xiaokaizip/lm5116-digital-power/c6t6-lm5116/Core/Src/oled.c

//
// Created by LaoZhu on 2022/3/3.
//

#include "oled.h"
#include "iic.h"
#include "data_type_conversion.h"
#include "stm32f1xx_hal.h"

const unsigned char F8X16[] = {
        0x00, 0x00, 0x00, 0x00, 0x00, 0x00, 0x00, 0x00, 0x00, 0x00, 0x00, 0x00, 0x00, 0x00, 0x00, 0x00,// 0
        0x00, 0x00, 0x00, 0xF8, 0x00, 0x00, 0x00, 0x00, 0x00, 0x00, 0x00, 0x33, 0x30, 0x00, 0x00, 0x00,//! 1
        0x00, 0x10, 0x0C, 0x06, 0x10, 0x0C, 0x06, 0x00, 0x00, 0x00, 0x00, 0x00, 0x00, 0x00, 0x00, 0x00,//" 2
        0x40, 0xC0, 0x78, 0x40, 0xC0, 0x78, 0x40, 0x00, 0x04, 0x3F, 0x04, 0x04, 0x3F, 0x04, 0x04, 0x00,//# 3
        0x00, 0x70, 0x88, 0xFC, 0x08, 0x30, 0x00, 0x00, 0x00, 0x18, 0x20, 0xFF, 0x21, 0x1E, 0x00, 0x00,//$ 4
        0xF0, 0x08, 0xF0, 0x00, 0xE0, 0x18, 0x00, 0x00, 0x00, 0x21, 0x1C, 0x03, 0x1E, 0x21, 0x1E, 0x00,//% 5
        0x00, 0xF0, 0x08, 0x88, 0x70, 0x00, 0x00, 0x00, 0x1E, 0x21, 0x23, 0x24, 0x19, 0x27, 0x21, 0x10,//& 6
        0x10, 0x16, 0x0E, 0x00, 0x00, 0x00, 0x00, 0x00, 0x00, 0x00, 0x00, 0x00, 0x00, 0x00, 0x00, 0x00,//' 7
        0x00, 0x00, 0x00, 0xE0, 0x18, 0x04, 0x02, 0x00, 0x00, 0x00, 0x00, 0x07, 0x18, 0x20, 0x40, 0x00,//( 8
        0x00, 0x02, 0x04, 0x18, 0xE0, 0x00, 0x00, 0x00, 0x00, 0x40, 0x20, 0x18, 0x07, 0x00, 0x00, 0x00,//) 9
        0x40, 0x40, 0x80, 0xF0, 0x80, 0x40, 0x40, 0x00, 0x02, 0x02, 0x01, 0x0F, 0x01, 0x02, 0x02, 0x00,//* 10
        0x00, 0x00, 0x00, 0xF0, 0x00, 0x00, 0x00, 0x00, 0x01, 0x01, 0x01, 0x1F, 0x01, 0x01, 0x01, 0x00,//+ 11
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
    IIC_Wait_Ask();
    IIC_Stop();
}

void WriteDat(unsigned char data) {
    IIC_Start();
    IIC_WriteByte(0x78);
    IIC_Wait_Ask();
    IIC_WriteByte(0x40);
    IIC_Wait_Ask();
    IIC_WriteByte(data);
    IIC_Wait_Ask();
    IIC_Stop();
}

void OLED_Init(void) {
    HAL_Delay(100);

    WriteCmd(0xAE); //display off
    WriteCmd(0x20); //Set Memory Addressing Mode
    WriteCmd(0x10); //00Horizontal Addressing Mode;01Vertical Addressing Mode;10Page Addressing Mode (RESET);
    WriteCmd(0xb0); //Set Page Start Address for Page Addressing Mode,0-7
    WriteCmd(0xc8); //Set COM Output Scan Direction
    WriteCmd(0x00); //---set low column address
    WriteCmd(0x10); //---set high column address
    WriteCmd(0x40); //--set start line address
    WriteCmd(0x81); //--set contrast control register
    WriteCmd(0xff); //亮度调节 0x00~0xff
    WriteCmd(0xa1); //--set segment re-map 0 to 127
    WriteCmd(0xa6); //--set normal display
    WriteCmd(0xa8); //--set multiplex ratio(1 to 64)
    WriteCmd(0x3F); //
    WriteCmd(0xa4); //0xa4,Output follows RAM content;0xa5,Output ignores RAM content
    WriteCmd(0xd3); //-set display offset
    WriteCmd(0x00); //-not offset
    WriteCmd(0xd5); //--set display clock divide ratio/oscillator frequency
    WriteCmd(0xf0); //--set divide ratio
    WriteCmd(0xd9); //--set pre-charge period
    WriteCmd(0x22); //
    WriteCmd(0xda); //--set com pins hardware configuration
    WriteCmd(0x12);
    WriteCmd(0xdb); //--set vcomh
    WriteCmd(0x20); //0x20,0.77xVcc
    WriteCmd(0x8d); //--set DC-DC enable
    WriteCmd(0x14); //
    WriteCmd(0xaf); //--turn on oled panel
}

void OLED_SetPos(unsigned char x, unsigned char y) {
    WriteCmd(0xb0 + y);
    WriteCmd(((x & 0xf0) >> 4) | 0x10);
    WriteCmd((x & 0x0f) | 0x01);
}

void OLED_Fill(unsigned char fill_Data) {
    unsigned char m, n;
    for (m = 0; m < 8; m++) {
        WriteCmd(0xb0 + m);       //page0-page1
        WriteCmd(0x00);     //low column start address
        WriteCmd(0x10);     //high column start address
        for (n = 0; n < 128; n++) {
            WriteDat(fill_Data);
        }
    }
}

void OLED_ShowStr(unsigned char x, unsigned char y, const char *ch) {
    unsigned char c = 0, i = 0, j = 0;
    while (ch[j] != '\0') {
        c = ch[j] - 32;
        if (x > 120) {
            x = 0;
            y++;
        }
        OLED_SetPos(x, y);
        for (i = 0; i < 8; i++)
            WriteDat(F8X16[c * 16 + i]);
        OLED_SetPos(x, y + 1);
        for (i = 0; i < 8; i++)
            WriteDat(F8X16[c * 16 + i + 8]);
        x += 8;
        j++;
    }
}

void OLED_ShowFloat(unsigned char x, unsigned char y, float num) {
    char string[20];
    numTostring(num, string);
    OLED_ShowStr(x, y, string);
}

void OLED_ShowMenu(float expect_voltage, float real_voltage) {
    OLED_ShowStr(0, 0, "Expect: ");
    OLED_ShowFloat(8 * 8, 0, expect_voltage);
    OLED_ShowStr(0, 2, "Real: ");
    OLED_ShowFloat(8 * 8, 2, real_voltage);
}
