xiaokaizip/lm5116-digital-power/c6t6-lm5116/Core/Inc/data_type_conversion.h

//
// Created by 86136 on 2022/10/10.
//

#ifndef C6T6_LM5116_DATA_TYPE_CONVERSION_H
#define C6T6_LM5116_DATA_TYPE_CONVERSION_H

void numTostring(float num, char str[10]);

#endif //C6T6_LM5116_DATA_TYPE_CONVERSION_H
