xiaokaizip/lm5116-digital-power/c6t6-lm5116/Core/Inc/key.h

//
// Created by 86136 on 2022/10/15.
//

#ifndef C6T6_LM5116_KEY_H
#define C6T6_LM5116_KEY_H

#include "main.h"

#define RESISTANCE_UP         1
#define RESISTANCE_DOWN       2
#define ENTER                 3
#define SELECT                4

#define VOLTAGE_UP            2
#define VOLTAGE_DOWN          1

uint8_t Enter_Key();


#endif //C6T6_LM5116_KEY_H
