xiaokaizip/lm5116-digital-power/c6t6-lm5116/Core/Inc/oled.h

//
// Created by LaoZhu on 2022/3/3.
//

#ifndef PROGRAM_OLED_H
#define PROGRAM_OLED_H

void OLED_Fill(unsigned char fill_Data);

void OLED_ShowStr(unsigned char x, unsigned char y, const char *ch);

void OLED_ShowFloat(unsigned char x, unsigned char y, float num);

void OLED_ShowMenu(float expect_voltage, float real_voltage);

void OLED_Init(void);

#endif //PROGRAM_OLED_H
