xiaokaizip/lm5116-digital-power/c6t6-lm5116/Core/Inc/printf.h

//
// Created by 86136 on 2022/8/23.
//

#ifndef RCT6_PRINTF_H
#define RCT6_PRINTF_H

int uint8Toint(uint8_t buff);

int uint16Toint(uint16_t buff);

int uint32Toint(uint32_t buff);

void uint8PrintIn(uint8_t num);

void uint16PrintIn(uint16_t num);

void uint32PrintIn(uint32_t num);

#endif //RCT6_PRINTF_H
