xiaokaizip/lm5116-digital-power/c6t6-lm5116/Core/Src/delay.c

/**
 * There is the function of delay in this file.
 */

#include "main.h"

static unsigned int delay_us_factor = 0;

void delayus(unsigned int xus) {
    delay_us_factor = SystemCoreClock / 1000000;
    unsigned int Ticks, Time_Old, Time_Now, Time_Count = 0;
    unsigned int Reload = SysTick->LOAD;
    Ticks = xus * delay_us_factor;
    Time_Old = SysTick->VAL;
    while (1) {
        Time_Now = SysTick->VAL;
        if (Time_Now != Time_Old) {
            if (Time_Now < Time_Old)
                Time_Count += Time_Old - Time_Now;
            else
                Time_Count += Reload - Time_Now + Time_Old;
            Time_Old = Time_Now;
            if (Time_Count >= Ticks)
                break;
        }
    }
}
