xiaokaizip/lm5116-digital-power/c6t6-lm5116/Core/Src/printf.c

#include "usart.h"
#include <math.h>

/**
 * 将8位的无符号整型转化为整型
 * @param buff
 * @return
 */
int uint8Toint(uint8_t buff) {
    int num = 0;
    for (int i = 0; i < 8; i++) {
        if (buff & (1 << i)) {
            num += pow(2, i);
        }
    }
    return num;
}

/**
 * 将16位的无符号整型转化为整型
 * @param buff
 * @return
 */
int uint16Toint(uint16_t buff) {

    int num = 0;
    for (int i = 0; i < 16; i++) {
        if (buff & (1 << i)) {
            num += pow(2, i);
        }
    }
    return num;
}

/**
 * 将32位的无符号整型转化为整型
 * @param buff
 * @return
 */
int uint32Toint(uint32_t buff) {

    int num = 0;
    for (int i = 0; i < 32; i++) {
        if (buff & (1 << i)) {
            num += pow(2, i);
        }
    }
    return num;
}

/**
 * 将8位的无符号数据转换为字符串，并通过串口输出(0~255)
 * @param buff
 */
void uint8PrintIn(uint8_t num) {
    char ch[10];
    int i = 0;
    while (1) {
        if (num < 10) {
            break;
        }
        ch[i] = '0' + num % 10;
        i++;
        num /= 10;

    }
    ch[i] = '0' + num % 10;
    for (int j = 0; j < (i + 1) / 2; j++) {
        char temp = ch[j];
        ch[j] = ch[i - j];
        ch[i - j] = temp;

    }
    HAL_UART_Transmit(&huart1, ch, i + 1, HAL_MAX_DELAY);
    HAL_UART_Transmit(&huart1, "\r\n", 2, HAL_MAX_DELAY);

}

/**
 * 将16位的无符号数据转换为字符串，并通过串口输出(0~65535)
 * @param buff
 */
void uint16PrintIn(uint16_t num) {
    char ch[10];
    int i = 0;
    while (1) {
        if (num < 10) {
            break;
        }
        ch[i] = '0' + num % 10;
        i++;
        num /= 10;

    }
    ch[i] = '0' + num % 10;
    for (int j = 0; j < (i + 1) / 2; j++) {
        char temp = ch[j];
        ch[j] = ch[i - j];
        ch[i - j] = temp;

    }
    HAL_UART_Transmit(&huart1, ch, i + 1, HAL_MAX_DELAY);
    HAL_UART_Transmit(&huart1, "\r\n", 2, HAL_MAX_DELAY);
}

/**
 * 将32位的无符号数据转换为字符串，并通过串口输出(0~4,294,967,295)
 * @param buff
 */
void uint32PrintIn(uint32_t num) {
    char ch[10];
    int i = 0;

    while (1) {
        if (num < 10) {
            break;
        }
        ch[i] = '0' + num % 10;
        i++;
        num /= 10;

    }
    ch[i] = '0' + num % 10;
    for (int j = 0; j < (i + 1) / 2; j++) {
        char temp = ch[j];
        ch[j] = ch[i - j];
        ch[i - j] = temp;

    }
    HAL_UART_Transmit(&huart1, ch, i + 1, HAL_MAX_DELAY);
    HAL_UART_Transmit(&huart1, "\r\n", 2, HAL_MAX_DELAY);
}
